monstro-das-bolachas/obdee-wan-canobi/revisions/00_WORK_R11_TRUE_DUAL_CANFD/kicad/teensy-41-true-dual-canfd-lin-r11_JARVIS_ROUTED_CLEAN_V2_GND_STITCH.kicad_sch

## KiCad design revisions/00_WORK_R11_TRUE_DUAL_CANFD/kicad/teensy-41-true-dual-canfd-lin-r11_JARVIS_ROUTED_CLEAN_V2_GND_STITCH.kicad_sch (2026-07-01)

Schematic: teensy-41-true-dual-canfd-lin-r11_JARVIS_ROUTED_CLEAN_V2_GND_STITCH.kicad_sch

Parts:
C1: 100uF_50V_INPUT; CP_Radial_D8.0mm_P3.50mm
C2: 100nF_50V_INPUT; C_0805_2012Metric_Pad1.18x1.45mm_HandSolder
C3: 330uF_16V_OUTPUT_LOW_ESR; CP_Radial_D8.0mm_P3.50mm
C4: 100nF_16V_OUTPUT; C_0805_2012Metric_Pad1.18x1.45mm_HandSolder
C5: 100nF_CAN_A_VDD_LOCAL; C_0805_2012Metric_Pad1.18x1.45mm_HandSolder
C6: 100nF_CAN_B_VDD_LOCAL; C_0805_2012Metric_Pad1.18x1.45mm_HandSolder
C7: 100nF_LIN_VSUP_LOCAL; C_0805_2012Metric_Pad1.18x1.45mm_HandSolder
C8: 22pF_Y1_OSC1; C_0805_2012Metric_Pad1.18x1.45mm_HandSolder
C9: 22pF_Y1_OSC2; C_0805_2012Metric_Pad1.18x1.45mm_HandSolder
C10: 22pF_Y2_OSC1; C_0805_2012Metric_Pad1.18x1.45mm_HandSolder
C11: 22pF_Y2_OSC2; C_0805_2012Metric_Pad1.18x1.45mm_HandSolder
C12: 100nF_U6_VDD_LOCAL; C_0805_2012Metric_Pad1.18x1.45mm_HandSolder
C13: 100nF_U7_VDD_LOCAL; C_0805_2012Metric_Pad1.18x1.45mm_HandSolder
D1: SMBJ24CA_TVS_12V; D_SMA
D2: SS34_BUCK_SCHOTTKY; D_SMA
D3: LIN_MASTER_PULLUP_DIODE_DNP; D_SMA; not fitted
D4: ESD_CAN_A_H_TVS_VERIFY; D_SMA
D5: ESD_CAN_A_L_TVS_VERIFY; D_SMA
D6: ESD_CAN_B_H_TVS_VERIFY; D_SMA
D7: ESD_CAN_B_L_TVS_VERIFY; D_SMA
D8: ESD_LIN_K_TVS_VERIFY; D_SMA
F1: POLYFUSE_500mA; Fuse_1206_3216Metric
J1: OBD2_PIGTAIL_16_WIRE_SOLDER_PADS; OBD2_PigtailPads_Manufacturing
J2: AUX_HEADER; PinHeader_1x08_P2.54mm_Vertical
JP1: LIN_MASTER_ENABLE_OPEN_0R_DNP; R_0805_2012Metric_Pad1.20x1.40mm_HandSolder; not fitted
L1: 33uH_3A_BUCK_INDUCTOR; L_Radial_D8.7mm_P5.00mm_Fastron_07HCP
MH1, MH2, MH3, MH4: M3; MountingHole_3.2mm_M3
R1: 10k_LIN_RX_PULLUP; R_0805_2012Metric_Pad1.20x1.40mm_HandSolder
R11: 100k_LIN_EN_PULLDOWN; R_0805_2012Metric_Pad1.20x1.40mm_HandSolder
R12: 10k_CAN_A_STBY_PULLUP; R_0805_2012Metric_Pad1.20x1.40mm_HandSolder
R13: 10k_CAN_B_STBY_PULLUP; R_0805_2012Metric_Pad1.20x1.40mm_HandSolder
R14: 10k_CANFD_A_NCS_PULLUP; R_0805_2012Metric_Pad1.20x1.40mm_HandSolder
R15: 10k_CANFD_B_NCS_PULLUP; R_0805_2012Metric_Pad1.20x1.40mm_HandSolder
R16: 1k_LIN_MASTER_PULLUP_DNP; R_0805_2012Metric_Pad1.20x1.40mm_HandSolder; not fitted
SR1, SR2: CABLE_STRAIN_RELIEF; MountingHole_3.2mm_M3
SW1: CAN_NORMAL_CROSS_DIP_8POS; SW_DIP_SPSTx08_Slide_9.78x22.5mm_W7.62mm_P2.54mm
SW2: LIN_K_SOURCE_DIP_8POS_SELECT_ONE; SW_DIP_SPSTx08_Slide_9.78x22.5mm_W7.62mm_P2.54mm
TP1: 12V; TestPoint_Pad_D1.5mm
TP2: 5V; TestPoint_Pad_D1.5mm
TP3: GND; TestPoint_Pad_D1.5mm
TP4: CAN_A_H; TestPoint_Pad_D1.5mm
TP5: CAN_A_L; TestPoint_Pad_D1.5mm
TP6: CAN_B_H; TestPoint_Pad_D1.5mm
TP7: CAN_B_L; TestPoint_Pad_D1.5mm
TP8: LIN_BUS; TestPoint_Pad_D1.5mm
TP9: AUX_LIN_K; TestPoint_Pad_D1.5mm
U1: TEENSY_4.1_MAIN_HEADERS_PJRC_AUDITED; Teensy_4.1_MainHeaders_PJRC_Audited
U2: MCP2562FD_CAN_A_3V3_IO; SOIC-8_3.9x4.9mm_P1.27mm
U3: MCP2562FD_CAN_B_3V3_IO; SOIC-8_3.9x4.9mm_P1.27mm
U4: TLIN1029DRQ1_LIN_3V3_LOGIC; SOIC-8_3.9x4.9mm_P1.27mm
U5: LM2596S-5.0_BUCK; TO-263-5_TabPin3
U6: MCP2518FD_A_SOIC14; SOIC-14_3.9x8.7mm_P1.27mm
U7: MCP2518FD_B_SOIC14; SOIC-14_3.9x8.7mm_P1.27mm
Y1, Y2: 40MHz_3225_VERIFY_CL; Crystal_SMD_3225-4Pin_3.2x2.5mm_HandSoldering

Notes on the sheet:
PCB-derived schematic catalog. Symbols are linked to PCB footprints for BOM/ERC proof. This is not yet a hand-reviewed functional wired schematic; use R11_PCB_DERIVED_NETLIST.md for pad/net authority.
